Seeed-Studio/OSHW-reCamera-Series/hardware/recamera-2002/base/b101-default/README.md

# B101 default base board

B101 is the base board shipped in standard reCamera 2002/2002w Basic products.

## Interfaces

- USB 2.0 Type-C for power, USB networking, and communication
- 10/100 Ethernet through a single-port transformer
- microSD card slot
- UART and debug/user controls exposed by the design

> [!WARNING]
> The B101 Ethernet port is not PoE. Continue to power the camera through
> USB-C when Ethernet is connected.

## Resources

- Editable revisions: [PCB](PCB/)
- [v1.2 schematic PDF](static/reCamera%20B101%20v1.2_SCH_PDF_240927.pdf)
- Enclosure files: [3D_Printed_Case](3D_Printed_Case/)

Match the files to the revision marking on the physical board before repair or
manufacture.
