Seeed-Studio/OSHW-reCamera-Series/hardware/recamera-2002/base/b201-vertical-usb-c/README-CN.md

# B201 垂直 USB-C 底板

[English](README.md) | 简体中文

B201 调整了标准有线接口的布局，使 USB-C 采用垂直安装方向。本目录为**参考/原型设计**，并非标准 reCamera 2002 基础版产品随附的底板。

该设计提供 USB-C、以太网、microSD 和 UART 功能。可编辑 KiCad 源文件位于 [PCB](PCB/)，外壳文件位于 [3D_Printed_Case](3D_Printed_Case/)。

部署前，请验证 USB 供电完整性、以太网磁性器件、机械间隙、热性能和 EMC。
