Seeed-Studio/OSHW-reCamera-Series/hardware/recamera-2002/products/gimbal/mechanical/recamera-gimbalcover-4040_20.stp

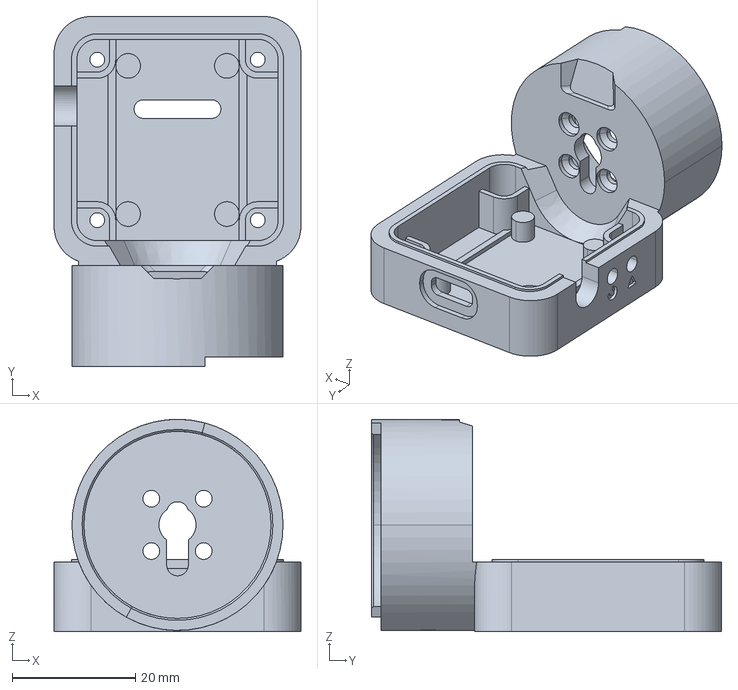
[picture p28: CAD file, 2024-12-10]
hardware/recamera-2002/products/gimbal/mechanical/recamera-gimbalcover-4040_20.stp
40.0 x 56.7 x 34.4 mm
