Seeed-Studio/OSHW-reCamera-Series/hardware/recamera-2002/products/gimbal/mechanical/brushlessmotor-ms3506_4.stp

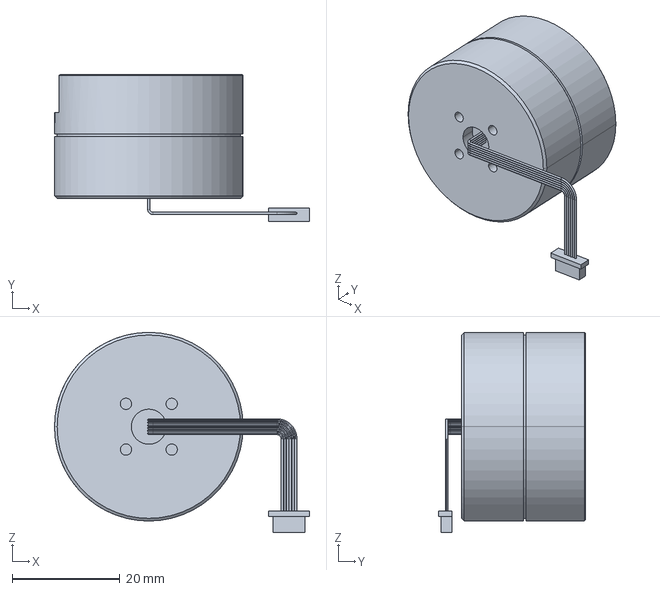
[picture p29: CAD file, 2024-12-10]
hardware/recamera-2002/products/gimbal/mechanical/brushlessmotor-ms3506_4.stp
47.3 x 27.3 x 37.1 mm
