Seeed-Studio/OSHW-reCamera-Series/hardware/recamera-2002/products/gimbal/mechanical/bottom-plate_10.stp

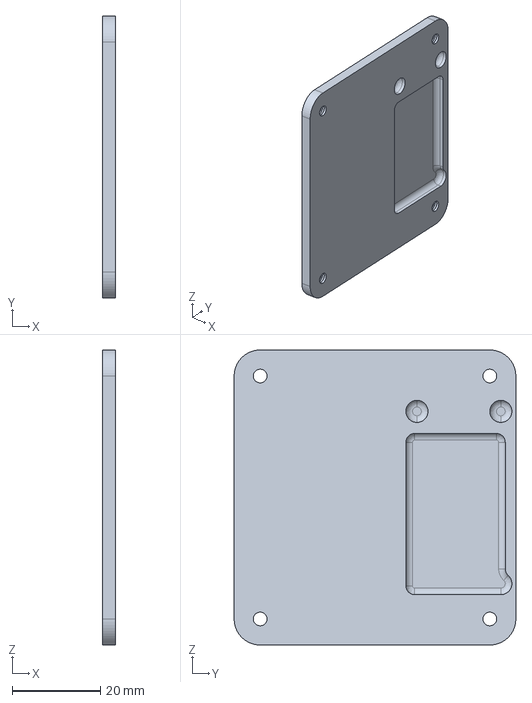
[picture p30: CAD file, 2024-12-10]
hardware/recamera-2002/products/gimbal/mechanical/bottom-plate_10.stp
3.00 x 63.8 x 66.8 mm
